bemcgarvey/CRSFtoPWM/firmware/src/sensorTask.h

/////////////////////////////////////////////////////
// Project: CRSFtoPWM                              //
// File: sensorTask.h                              //
// Target: ATSAMD21E18A                            // 
// Compiler: XC32                                  //
// Author: Brad McGarvey                           //
// License: GNU General Public License v3.0        //
// Description: sensor task handler                //
/////////////////////////////////////////////////////

#ifndef SENSORTASK_H
#define	SENSORTASK_H

#ifdef	__cplusplus
extern "C" {
#endif

    void sensorTask(void *pvParameter);

#ifdef	__cplusplus
}
#endif

#endif	/* SENSORTASK_H */
