bemcgarvey/CRSFtoPWM/firmware/src/config/default/peripheral/port/plib_port.h

/*******************************************************************************
  PORT PLIB

  Company:
    Microchip Technology Inc.

  File Name:
    plib_port.h

  Summary:
    PORT PLIB Header File

  Description:
    This file provides an interface to control and interact with PORT-I/O
    Pin controller module.

*******************************************************************************/

/*******************************************************************************
* Copyright (C) 2018 Microchip Technology Inc. and its subsidiaries.
*
* Subject to your compliance with these terms, you may use Microchip software
* and any derivatives exclusively with Microchip products. It is your
* responsibility to comply with third party license terms applicable to your
* use of third party software (including open source software) that may
* accompany Microchip software.
*
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
* IN NO EVENT WILL MICROCHIP BE LIABLE FOR ANY INDIRECT, SPECIAL, PUNITIVE,
* INCIDENTAL OR CONSEQUENTIAL LOSS, DAMAGE, COST OR EXPENSE OF ANY KIND
* WHATSOEVER RELATED TO THE SOFTWARE, HOWEVER CAUSED, EVEN IF MICROCHIP HAS
* BEEN ADVISED OF THE POSSIBILITY OR THE DAMAGES ARE FORESEEABLE. TO THE
* FULLEST EXTENT ALLOWED BY LAW, MICROCHIP'S TOTAL LIABILITY ON ALL CLAIMS IN
* ANY WAY RELATED TO THIS SOFTWARE WILL NOT EXCEED THE AMOUNT OF FEES, IF ANY,
* THAT YOU HAVE PAID DIRECTLY TO MICROCHIP FOR THIS SOFTWARE.
*******************************************************************************/

#ifndef PLIB_PORT_H
#define PLIB_PORT_H

// *****************************************************************************
// *****************************************************************************
// Section: Included Files
// *****************************************************************************
// *****************************************************************************

#include "device.h"
#include <stdint.h>
#include <stdbool.h>
#include <stddef.h>

// DOM-IGNORE-BEGIN
#ifdef __cplusplus  // Provide C++ Compatibility
    extern "C" {
#endif
// DOM-IGNORE-END

// *****************************************************************************
// *****************************************************************************
// Section: Data types and constants
// *****************************************************************************
// *****************************************************************************

/*** Macros for LED pin ***/
#define LED_Set()               (PORT_REGS->GROUP[0].PORT_OUTSET = ((uint32_t)1U << 15U))
#define LED_Clear()             (PORT_REGS->GROUP[0].PORT_OUTCLR = ((uint32_t)1U << 15U))
#define LED_Toggle()            (PORT_REGS->GROUP[0].PORT_OUTTGL = ((uint32_t)1U << 15U))
#define LED_OutputEnable()      (PORT_REGS->GROUP[0].PORT_DIRSET = ((uint32_t)1U << 15U))
#define LED_InputEnable()       (PORT_REGS->GROUP[0].PORT_DIRCLR = ((uint32_t)1U << 15U))
#define LED_Get()               (((PORT_REGS->GROUP[0].PORT_IN >> 15U)) & 0x01U)
#define LED_PIN                  PORT_PIN_PA15

// *****************************************************************************
/* PORT Group

  Summary:
    Identifies the port groups available on the device.

  Description:
    These macros identifies all the ports groups that are available on this
    device.

  Remarks:
    The caller should not use the constant expressions assigned to any of
    the preprocessor macros as these may vary between devices.

    Port groups shown here are the ones available on the selected device. Not
    all ports groups are implemented. Refer to the device specific datasheet
    for more details. The MHC will generate these macros with the port
    groups that are available on the device.
*/

/* Group 0 */
#define PORT_GROUP_0 (PORT_BASE_ADDRESS + (0U * 0x80U))


/* Helper macros to get port information from the pin */
#define GET_PORT_GROUP(pin)  ((PORT_GROUP)(PORT_BASE_ADDRESS + (0x80U * (((uint32_t)pin) >> 5U))))
#define GET_PIN_MASK(pin)   (((uint32_t)(0x1U)) << (((uint32_t)pin) & 0x1FU))

/* Named type for port group */
typedef uint32_t PORT_GROUP;


typedef enum
{
PERIPHERAL_FUNCTION_A = 0x0,
PERIPHERAL_FUNCTION_B = 0x1,
PERIPHERAL_FUNCTION_C = 0x2,
PERIPHERAL_FUNCTION_D = 0x3,
PERIPHERAL_FUNCTION_E = 0x4,
PERIPHERAL_FUNCTION_F = 0x5,
PERIPHERAL_FUNCTION_G = 0x6,
PERIPHERAL_FUNCTION_H = 0x7,

}PERIPHERAL_FUNCTION;

// *****************************************************************************
/* PORT Pins

  Summary:
    Identifies the available Ports pins.

  Description:
    This enumeration identifies all the ports pins that are available on this
    device.

  Remarks:
    The caller should not use the constant expressions assigned to any of
    the enumeration constants as these may vary between devices.

    Port pins shown here are the ones available on the selected device. Not
    all ports pins within a port group are implemented. Refer to the device
    specific datasheet for more details.
*/

typedef enum
{
    /* PA00 pin */
    PORT_PIN_PA00 = 0U,

    /* PA01 pin */
    PORT_PIN_PA01 = 1U,

    /* PA02 pin */
    PORT_PIN_PA02 = 2U,

    /* PA03 pin */
    PORT_PIN_PA03 = 3U,

    /* PA04 pin */
    PORT_PIN_PA04 = 4U,

    /* PA05 pin */
    PORT_PIN_PA05 = 5U,

    /* PA06 pin */
    PORT_PIN_PA06 = 6U,

    /* PA07 pin */
    PORT_PIN_PA07 = 7U,

    /* PA08 pin */
    PORT_PIN_PA08 = 8U,

    /* PA09 pin */
    PORT_PIN_PA09 = 9U,

    /* PA10 pin */
    PORT_PIN_PA10 = 10U,

    /* PA11 pin */
    PORT_PIN_PA11 = 11U,

    /* PA14 pin */
    PORT_PIN_PA14 = 14U,

    /* PA15 pin */
    PORT_PIN_PA15 = 15U,

    /* PA16 pin */
    PORT_PIN_PA16 = 16U,

    /* PA17 pin */
    PORT_PIN_PA17 = 17U,

    /* PA18 pin */
    PORT_PIN_PA18 = 18U,

    /* PA19 pin */
    PORT_PIN_PA19 = 19U,

    /* PA22 pin */
    PORT_PIN_PA22 = 22U,

    /* PA23 pin */
    PORT_PIN_PA23 = 23U,

    /* PA24 pin */
    PORT_PIN_PA24 = 24U,

    /* PA25 pin */
    PORT_PIN_PA25 = 25U,

    /* PA27 pin */
    PORT_PIN_PA27 = 27U,

    /* PA28 pin */
    PORT_PIN_PA28 = 28U,

    /* PA30 pin */
    PORT_PIN_PA30 = 30U,

    /* PA31 pin */
    PORT_PIN_PA31 = 31U,

    /* This element should not be used in any of the PORT APIs.
     * It will be used by other modules or application to denote that none of
     * the PORT Pin is used */
    PORT_PIN_NONE = 65535U,

} PORT_PIN;

// *****************************************************************************
// *****************************************************************************
// Section: Generated API based on pin configurations done in Pin Manager
// *****************************************************************************
// *****************************************************************************
// *****************************************************************************
/* Function:
    void PORT_Initialize(void)

  Summary:
    Initializes the PORT Library.

  Description:
    This function initializes all ports and pins as configured in the
    MHC Pin Manager.

  Precondition:
    None.

  Parameters:
    None.

  Returns:
    None.

  Example:
    <code>

    PORT_Initialize();

    </code>

  Remarks:
    The function should be called once before calling any other PORTS PLIB
    functions.
*/

void PORT_Initialize(void);

// *****************************************************************************
// *****************************************************************************
// Section: PORT APIs which operates on multiple pins of a group
// *****************************************************************************
// *****************************************************************************

// *****************************************************************************
/* Function:
    uint32_t PORT_GroupRead(PORT_GROUP group)

  Summary:
    Read all the I/O pins in the specified port group.

  Description:
    The function reads the hardware pin state of all pins in the specified group
    and returns this as a 32 bit value. Each bit in the 32 bit value represent a
    pin. For example, bit 0 in group 0 will represent pin PA0. Bit 1 will
    represent PA1 and so on. The application should only consider the value of
    the port group pins which are implemented on the device.

  Precondition:
    The PORT_Initialize() function should have been called. Input buffer
    (INEN bit in the Pin Configuration register) should be enabled in MHC.

  Parameters:
    group - One of the IO groups from the enum PORT_GROUP.

  Returns:
    A 32-bit value representing the hardware state of of all the I/O pins in the
    selected port group.

  Example:
    <code>

    uint32_t value;
    value = PORT_Read(PORT_GROUP_C);

    </code>

  Remarks:
    None.
*/

uint32_t PORT_GroupRead(PORT_GROUP group);

// *****************************************************************************
/* Function:
    uint32_t PORT_GroupLatchRead(PORT_GROUP group)

  Summary:
    Read the data driven on all the I/O pins of the selected port group.

  Description:
    The function will return a 32-bit value representing the logic levels being
    driven on the output pins within the group. The function will not sample the
    actual hardware state of the output pin. Each bit in the 32-bit return value
    will represent one of the 32 port pins within the group. The application
    should only consider the value of the pins which are available on the
    device.

  Precondition:
    The PORT_Initialize() function should have been called.

  Parameters:
    group - One of the IO groups from the enum PORT_GROUP.

  Returns:
    A 32-bit value representing the output state of of all the I/O pins in the
    selected port group.

  Example:
    <code>

    uint32_t value;
    value = PORT_GroupLatchRead(PORT_GROUP_C);

    </code>

  Remarks:
    None.
*/

uint32_t PORT_GroupLatchRead(PORT_GROUP group);

// *****************************************************************************
/* Function:
    void PORT_GroupWrite(PORT_GROUP group, uint32_t mask, uint32_t value);

  Summary:
    Write value on the masked pins of the selected port group.

  Description:
    This function writes the value contained in the value parameter to the
    port group. Port group pins which are configured for output will be updated.
    The mask parameter provides additional control on the bits in the group to
    be affected. Setting a bit to 1 in the mask will cause the corresponding
    bit in the port group to be updated. Clearing a bit in the mask will cause
    that corresponding bit in the group to stay unaffected. For example,
    setting a mask value 0xFFFFFFFF will cause all bits in the port group
    to be updated. Setting a value 0x3 will only cause port group bit 0 and
    bit 1 to be updated.

    For port pins which are not configured for output and have the pull feature
    enabled, this function will affect pull value (pull up or pull down). A bit
    value of 1 will enable the pull up. A bit value of 0 will enable the pull
    down.

  Precondition:
    The PORT_Initialize() function should have been called.

  Parameters:
    group - One of the IO groups from the enum PORT_GROUP.

    mask  - A 32 bit value in which positions of 0s and 1s decide
             which IO pins of the selected port group will be written.
             1's - Will write to corresponding IO pins.
             0's - Will remain unchanged.

    value - Value which has to be written/driven on the I/O
             lines of the selected port for which mask bits are '1'.
             Values for the corresponding mask bit '0' will be ignored.
             Refer to the function description for effect on pins
             which are not configured for output.

  Returns:
    None.

  Example:
    <code>

    PORT_GroupWrite(PORT_GROUP_C, 0x0F, 0xF563D453);

    </code>

  Remarks:
    None.
*/

void PORT_GroupWrite(PORT_GROUP group, uint32_t mask, uint32_t value);

// *****************************************************************************
/* Function:
    void PORT_GroupSet(PORT_GROUP group, uint32_t mask)

  Summary:
    Set the selected IO pins of a group.

  Description:
    This function sets (drives a logic high) on the selected output pins of a
    group. The mask parameter control the pins to be updated. A mask bit
    position with a value 1 will cause that corresponding port pin to be set. A
    mask bit position with a value 0 will cause the corresponding port pin to
    stay un-affected.

  Precondition:
    The PORT_Initialize() function should have been called.

  Parameters:
    group - One of the IO ports from the enum PORT_GROUP.
    mask - A 32 bit value in which a bit represent a pin in the group. If the
    value of the bit is 1, the corresponding port pin will driven to logic 1. If
    the value of the bit is 0. the corresponding port pin will stay un-affected.

  Returns:
    None.

  Example:
    <code>

    PORT_GroupSet(PORT_GROUP_C, 0x00A0);

    </code>

  Remarks:
    If the port pin within the the group is not configured for output and has
    the pull feature enabled, driving a logic 1 on this pin will cause the pull
    up to be enabled.
*/

void PORT_GroupSet(PORT_GROUP group, uint32_t mask);

// *****************************************************************************
/* Function:
    void PORT_GroupClear(PORT_GROUP group, uint32_t mask)

  Summary:
    Clears the selected IO pins of a group.

  Description:
    This function clears (drives a logic 0) on the selected output pins of a
    group. The mask parameter control the pins to be updated. A mask bit
    position with a value 1 will cause that corresponding port pin to be clear.
    A mask bit position with a value 0 will cause the corresponding port pin to
    stay un-affected.

  Precondition:
    The PORT_Initialize() function should have been called.

  Parameters:
    group - One of the IO ports from the enum PORT_GROUP.
    mask - A 32 bit value in which a bit represent a pin in the group. If the
    value of the bit is 1, the corresponding port pin will driven to logic 0. If
    the value of the bit is 0. the corresponding port pin will stay un-affected.

  Returns:
    None.

  Example:
    <code>

    PORT_GroupClear(PORT_GROUP_C, 0x00A0);

    </code>

  Remarks:
    If the port pin within the the group is not configured for output and has
    the pull feature enabled, driving a logic 0 on this pin will cause the pull
    down to be enabled.
*/

void PORT_GroupClear(PORT_GROUP group, uint32_t mask);

// *****************************************************************************
/* Function:
    void PORT_GroupToggle(PORT_GROUP group, uint32_t mask)

  Summary:
    Toggles the selected IO pins of a group.

  Description:
    This function toggles the selected output pins of a group. The mask
    parameter control the pins to be updated. A mask bit position with a value 1
    will cause that corresponding port pin to be toggled.  A mask bit position
    with a value 0 will cause the corresponding port pin to stay un-affected.

  Precondition:
    The PORT_Initialize() function should have been called.

  Parameters:
    group - One of the IO ports from the enum PORT_GROUP.
    mask - A 32 bit value in which a bit represent a pin in the group. If the
    value of the bit is 1, the corresponding port pin will be toggled. If the
    value of the bit is 0. the corresponding port pin will stay un-affected.

  Returns:
    None.

  Example:
    <code>

    PORT_GroupToggle(PORT_GROUP_C, 0x00A0);

    </code>

  Remarks:
    If the port pin within the the group is not configured for output and has
    the pull feature enabled, driving a logic 0 on this pin will cause the pull
    down to be enabled. Driving a logic 1 on this pin will cause the pull up to
    be enabled.
*/

void PORT_GroupToggle(PORT_GROUP group, uint32_t mask);

// *****************************************************************************
/* Function:
    void PORT_GroupInputEnable(PORT_GROUP group, uint32_t mask)

  Summary:
    Configures the selected IO pins of a group as input.

  Description:
    This function configures the selected IO pins of a group as input. The pins
    to be configured as input are selected by setting the corresponding bits in
    the mask parameter to 1.

  Precondition:
    The PORT_Initialize() function should have been called.

  Parameters:
    group - One or more of the of the IO ports from the enum PORT_GROUP.
    mask - A 32 bit value in which a bit represents a pin in the group. If the
    value of the bit is 1, the corresponding port pin will be configured as
    input. If the value of the bit is 0. the corresponding port pin will stay
    un-affected.

  Returns:
    None.

  Example:
    <code>

    PORT_GroupInputEnable(PORT_GROUP_C, 0x00A0);

    </code>

  Remarks:
   None.
*/

void PORT_GroupInputEnable(PORT_GROUP group, uint32_t mask);

// *****************************************************************************
/* Function:
    void PORT_GroupOutputEnable(PORT_GROUP group, uint32_t mask)

  Summary:
    Configures the selected IO pins of a group as output.

  Description:
    This function configures the selected IO pins of a group as output. The pins
    to be configured as output are selected by setting the corresponding bits in
    the mask parameter to 1.

  Precondition:
    The PORT_Initialize() function should have been called.

  Parameters:
    group - One or more of the of the IO ports from the enum PORT_GROUP.
    mask - A 32 bit value in which a bit represents a pin in the group. If the
    value of the bit is 1, the corresponding port pin will be configured as
    output. If the value of the bit is 0. the corresponding port pin will stay
    un-affected.

  Returns:
    None.

  Example:
    <code>

    PORT_GroupOutputEnable(PORT_GROUP_C, 0x00A0);

    </code>

  Remarks:
    None.
*/

void PORT_GroupOutputEnable(PORT_GROUP group, uint32_t mask);

// *****************************************************************************
/* Function:
    void PORT_PinPeripheralFunctionConfig(PORT_PIN pin, PERIPHERAL_FUNCTION function)

  Summary:
    Configures the peripheral function on the selected port pin

  Description:
    This function configures the selected peripheral function on the given port pin.

  Remarks:
    None
*/
void PORT_PinPeripheralFunctionConfig(PORT_PIN pin, PERIPHERAL_FUNCTION function);

// *****************************************************************************
/* Function:
    void PORT_PinGPIOConfig(PORT_PIN pin)

  Summary:
    Configures the selected pin as GPIO

  Description:
    This function configures the given pin as GPIO.

  Remarks:
    None
*/
void PORT_PinGPIOConfig(PORT_PIN pin);

// *****************************************************************************
// *****************************************************************************
// Section: PORT APIs which operates on one pin at a time
// *****************************************************************************
// *****************************************************************************

// *****************************************************************************
/* Function:
    void PORT_PinWrite(PORT_PIN pin, bool value)

  Summary:
    Writes the specified value to the selected pin.

  Description:
    This function writes/drives the "value" on the selected I/O line/pin.

  Precondition:
    The PORT_Initialize() function should have been called once.

  Parameters:
    pin - One of the IO pins from the enum PORT_PIN.
    value - value to be written on the selected pin.
            true  = set pin to high (1).
            false = clear pin to low (0).

  Returns:
    None.

  Example:
    <code>

    bool value = true;
    PORT_PinWrite(PORT_PIN_PB3, value);

    </code>

  Remarks:
    Calling this function with an input pin with the pull-up/pull-down feature
    enabled will affect the pull-up/pull-down configuration. If the value is
    false, the pull-down will be enabled. If the value is true, the pull-up will
    be enabled.
*/

static inline void PORT_PinWrite(PORT_PIN pin, bool value)
{
    PORT_GroupWrite(GET_PORT_GROUP(pin),
                    GET_PIN_MASK(pin),
                    (value ? GET_PIN_MASK(pin) : 0U));
}


// *****************************************************************************
/* Function:
    bool PORT_PinRead(PORT_PIN pin)

  Summary:
    Read the selected pin value.

  Description:
    This function reads the present state at the selected input pin.  The
    function can also be called to read the value of an output pin if input
    sampling on the output pin is enabled in MHC. If input synchronization on
    the pin is disabled in MHC, the function will cause a 2 PORT Clock cycles
    delay. Enabling the synchronization eliminates the delay but will increase
    power consumption.

  Precondition:
    The PORT_Initialize() function should have been called. Input buffer
    (INEN bit in the Pin Configuration register) should be enabled in MHC.

  Parameters:
    pin - the port pin whose state needs to be read.

  Returns:
    true - the state at the pin is a logic high.
    false - the state at the pin is a logic low.

  Example:
    <code>

    bool value;
    value = PORT_PinRead(PORT_PIN_PB3);

    </code>

  Remarks:
    None.
*/

static inline bool PORT_PinRead(PORT_PIN pin)
{
    return ((PORT_GroupRead(GET_PORT_GROUP(pin)) & GET_PIN_MASK(pin)) != 0U);
}


// *****************************************************************************
/* Function:
    bool PORT_PinLatchRead(PORT_PIN pin)

  Summary:
    Read the value driven on the selected pin.

  Description:
    This function reads the data driven on the selected I/O line/pin. The
    function does not sample the state of the hardware pin. It only returns the
    value that is written to output register. Refer to the PORT_PinRead()
    function if the state of the output pin needs to be read.

  Precondition:
    The PORT_Initialize() function should have been called.

  Parameters:
    pin - One of the IO pins from the enum PORT_PIN.

  Returns:
    true - the present value in the output latch is a logic high.
    false - the present value in the output latch is a logic low.

  Example:
    <code>

    bool value;
    value = PORT_PinLatchRead(PORT_PIN_PB3);

    </code>

  Remarks:
    To read actual pin value, PIN_Read API should be used.
*/

static inline bool PORT_PinLatchRead(PORT_PIN pin)
{
    return ((PORT_GroupLatchRead(GET_PORT_GROUP(pin)) & GET_PIN_MASK(pin)) != 0U);
}


// *****************************************************************************
/* Function:
    void PORT_PinToggle(PORT_PIN pin)

  Summary:
    Toggles the selected pin.

  Description:
    This function toggles/inverts the present value on the selected I/O line/pin.

  Precondition:
    The PORT_Initialize() function should have been called.

  Parameters:
    pin - One of the IO pins from the enum PORT_PIN.

  Returns:
    None.

  Example:
    <code>

    PORT_PinToggle(PORT_PIN_PB3);

    </code>

  Remarks:
    None.
*/

static inline void PORT_PinToggle(PORT_PIN pin)
{
    PORT_GroupToggle(GET_PORT_GROUP(pin), GET_PIN_MASK(pin));
}


// *****************************************************************************
/* Function:
    void PORT_PinSet(PORT_PIN pin)

  Summary:
    Sets the selected pin.

  Description:
    This function drives a logic 1 on the selected I/O line/pin.

  Precondition:
    The PORT_Initialize() function should have been called.

  Parameters:
    pin - One of the IO pins from the enum PORT_PIN.

  Returns:
    None.

  Example:
    <code>

    PORT_PinSet(PORT_PIN_PB3);

    </code>

  Remarks:
    None.
*/

static inline void PORT_PinSet(PORT_PIN pin)
{
    PORT_GroupSet(GET_PORT_GROUP(pin), GET_PIN_MASK(pin));
}


// *****************************************************************************
/* Function:
    void PORT_PinClear(PORT_PIN pin)

  Summary:
    Clears the selected pin.

  Description:
    This function drives a logic 0 on the selected I/O line/pin.

  Precondition:
    The PORT_Initialize() function should have been called.

  Parameters:
    pin - One of the IO pins from the enum PORT_PIN.

  Returns:
    None.

  Example:
    <code>

    PORT_PinClear(PORT_PIN_PB3);

    </code>

  Remarks:
    None.
*/

static inline void PORT_PinClear(PORT_PIN pin)
{
    PORT_GroupClear(GET_PORT_GROUP(pin), GET_PIN_MASK(pin));
}


// *****************************************************************************
/* Function:
    void PORT_PinInputEnable(PORT_PIN pin)

  Summary:
    Configures the selected IO pin as input.

  Description:
    This function configures the selected IO pin as input. This function
    override the MHC input output pin settings.

  Precondition:
    The PORT_Initialize() function should have been called.

  Parameters:
    pin - One of the IO pins from the enum PORT_PIN.

  Returns:
    None.

  Example:
    <code>

    PORT_PinInputEnable(PORT_PIN_PB3);

    </code>

  Remarks:
    None.
*/

static inline void PORT_PinInputEnable(PORT_PIN pin)
{
    PORT_GroupInputEnable(GET_PORT_GROUP(pin), GET_PIN_MASK(pin));
}


// *****************************************************************************
/* Function:
    void PORT_PinOutputEnable(PORT_PIN pin)

  Summary:
    Enables selected IO pin as output.

  Description:
    This function enables selected IO pin as output. Calling this function will
    override the MHC input output pin configuration.

  Precondition:
    The PORT_Initialize() function should have been called.

  Parameters:
    pin - One of the IO pins from the enum PORT_PIN.

  Returns:
    None.

  Example:
    <code>

    PORT_PinOutputEnable(PORT_PIN_PB3);

    </code>

  Remarks:
    None.
*/

static inline void PORT_PinOutputEnable(PORT_PIN pin)
{
    PORT_GroupOutputEnable(GET_PORT_GROUP(pin), GET_PIN_MASK(pin));
}

// DOM-IGNORE-BEGIN
#ifdef __cplusplus  // Provide C++ Compatibility

}

#endif
// DOM-IGNORE-END
#endif // PLIB_PORT_H
