bemcgarvey/CRSFtoPWM/firmware/src/config/default/peripheral/adc/plib_adc.c

/*******************************************************************************
  Analog-to-Digital Converter(ADC) PLIB

  Company
    Microchip Technology Inc.

  File Name
    plib_adc.c

  Summary
    ADC PLIB Implementation File.

  Description
    This file defines the interface to the ADC peripheral library. This
    library provides access to and control of the associated peripheral
    instance.

  Remarks:
    None.

*******************************************************************************/

// DOM-IGNORE-BEGIN
/*******************************************************************************
* Copyright (C) 2018 Microchip Technology Inc. and its subsidiaries.
*
* Subject to your compliance with these terms, you may use Microchip software
* and any derivatives exclusively with Microchip products. It is your
* responsibility to comply with third party license terms applicable to your
* use of third party software (including open source software) that may
* accompany Microchip software.
*
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
* IN NO EVENT WILL MICROCHIP BE LIABLE FOR ANY INDIRECT, SPECIAL, PUNITIVE,
* INCIDENTAL OR CONSEQUENTIAL LOSS, DAMAGE, COST OR EXPENSE OF ANY KIND
* WHATSOEVER RELATED TO THE SOFTWARE, HOWEVER CAUSED, EVEN IF MICROCHIP HAS
* BEEN ADVISED OF THE POSSIBILITY OR THE DAMAGES ARE FORESEEABLE. TO THE
* FULLEST EXTENT ALLOWED BY LAW, MICROCHIP'S TOTAL LIABILITY ON ALL CLAIMS IN
* ANY WAY RELATED TO THIS SOFTWARE WILL NOT EXCEED THE AMOUNT OF FEES, IF ANY,
* THAT YOU HAVE PAID DIRECTLY TO MICROCHIP FOR THIS SOFTWARE.
*******************************************************************************/
// DOM-IGNORE-END

// *****************************************************************************
// *****************************************************************************
// Section: Included Files
// *****************************************************************************
// *****************************************************************************
/* This section lists the other files that are included in this file.
*/

#include "plib_adc.h"
#include "interrupts.h"

// *****************************************************************************
// *****************************************************************************
// Section: Global Data
// *****************************************************************************
// *****************************************************************************

#define ADC_LINEARITY0_POS  (27U)
#define ADC_LINEARITY0_Msk   ((0x1FUL << ADC_LINEARITY0_POS))

#define ADC_LINEARITY1_POS  (0U)
#define ADC_LINEARITY1_Msk   ((0x7U << ADC_LINEARITY1_POS))

#define ADC_BIASCAL_POS  (3U)
#define ADC_BIASCAL_Msk   ((0x7U << ADC_BIASCAL_POS))

// *****************************************************************************
// *****************************************************************************
// Section: ADC Implementation
// *****************************************************************************
// *****************************************************************************

// *****************************************************************************
/* Initialize ADC module */
void ADC_Initialize( void )
{
    /* Reset ADC */
    ADC_REGS->ADC_CTRLA = ADC_CTRLA_SWRST_Msk;

    while((ADC_REGS->ADC_STATUS & ADC_STATUS_SYNCBUSY_Msk)!= 0U)
    {
        /* Wait for Synchronization */
    }

    uint32_t adc_linearity0 = (((*(uint32_t*)OTP4_ADDR) & ADC_LINEARITY0_Msk) >> ADC_LINEARITY0_POS);
    uint32_t adc_linearity1 = (((*(uint32_t*)(OTP4_ADDR + 4U)) & ADC_LINEARITY1_Msk) >> ADC_LINEARITY1_POS);

    /* Write linearity calibration and bias calibration */
    ADC_REGS->ADC_CALIB = (uint16_t)((ADC_CALIB_LINEARITY_CAL(adc_linearity0 | (adc_linearity1 << 5U))) \
        | ADC_CALIB_BIAS_CAL((((*(uint32_t*)(OTP4_ADDR + 4U)) & ADC_BIASCAL_Msk) >> ADC_BIASCAL_POS)));

    /* Sampling length */
    ADC_REGS->ADC_SAMPCTRL = ADC_SAMPCTRL_SAMPLEN(3U);

    /* reference */
    ADC_REGS->ADC_REFCTRL = ADC_REFCTRL_REFSEL_INTVCC1;

    /* positive and negative input pins */
    ADC_REGS->ADC_INPUTCTRL = (uint32_t) ADC_POSINPUT_PIN0 | (uint32_t) ADC_NEGINPUT_GND \
        | ADC_INPUTCTRL_INPUTSCAN(0U) | ADC_INPUTCTRL_INPUTOFFSET(0U) | ADC_INPUTCTRL_GAIN_DIV2;
    while((ADC_REGS->ADC_STATUS & ADC_STATUS_SYNCBUSY_Msk)!= 0U)
    {
        /* Wait for Synchronization */
    }

    /* Prescaler, Resolution & Operation Mode */
    ADC_REGS->ADC_CTRLB = ADC_CTRLB_PRESCALER_DIV64 | ADC_CTRLB_RESSEL_12BIT ;
    while((ADC_REGS->ADC_STATUS & ADC_STATUS_SYNCBUSY_Msk)!= 0U)
    {
        /* Wait for Synchronization */
    }

    /* Clear all interrupt flags */
    ADC_REGS->ADC_INTFLAG = ADC_INTFLAG_Msk;

    while((ADC_REGS->ADC_STATUS & ADC_STATUS_SYNCBUSY_Msk) != 0U)
    {
        /* Wait for Synchronization */
    }
}

/* Enable ADC module */
void ADC_Enable( void )
{
    ADC_REGS->ADC_CTRLA |= ADC_CTRLA_ENABLE_Msk;
    while((ADC_REGS->ADC_STATUS & ADC_STATUS_SYNCBUSY_Msk) != 0U)
    {
        /* Wait for Synchronization */
    }
}

/* Disable ADC module */
void ADC_Disable( void )
{
    ADC_REGS->ADC_CTRLA = ((ADC_REGS->ADC_CTRLA) & (uint8_t)(~ADC_CTRLA_ENABLE_Msk));
    while((ADC_REGS->ADC_STATUS & ADC_STATUS_SYNCBUSY_Msk) != 0U)
    {
        /* Wait for Synchronization */
    }
}

/* Configure channel input */
void ADC_ChannelSelect( ADC_POSINPUT positiveInput, ADC_NEGINPUT negativeInput )
{
    /* Configure positive and negative input pins */
    uint32_t channel;
    channel = ADC_REGS->ADC_INPUTCTRL;
    channel &= ~(ADC_INPUTCTRL_MUXPOS_Msk | ADC_INPUTCTRL_MUXNEG_Msk);
    channel |= (uint32_t) positiveInput | (uint32_t) negativeInput;
    ADC_REGS->ADC_INPUTCTRL = channel;

    while((ADC_REGS->ADC_STATUS & ADC_STATUS_SYNCBUSY_Msk) != 0U)
    {
        /* Wait for Synchronization */
    }
}

/* Start the ADC conversion by SW */
void ADC_ConversionStart( void )
{
    /* Start conversion */
    ADC_REGS->ADC_SWTRIG |= ADC_SWTRIG_START_Msk;

    while((ADC_REGS->ADC_STATUS & ADC_STATUS_SYNCBUSY_Msk) != 0U)
    {
        /* Wait for Synchronization */
    }
}

/* Configure window comparison threshold values */
void ADC_ComparisonWindowSet(uint16_t low_threshold, uint16_t high_threshold)
{
    ADC_REGS->ADC_WINLT = low_threshold;
    while((ADC_REGS->ADC_STATUS & ADC_STATUS_SYNCBUSY_Msk) != 0U)
    {
        /* Wait for Synchronization */
    }    
    ADC_REGS->ADC_WINUT = high_threshold;
    while((ADC_REGS->ADC_STATUS & ADC_STATUS_SYNCBUSY_Msk) != 0U)
    {
        /* Wait for Synchronization */
    }
}

void ADC_WindowModeSet(ADC_WINMODE mode)
{
    ADC_REGS->ADC_WINCTRL = (uint8_t)mode << ADC_WINCTRL_WINMODE_Pos;
    while((ADC_REGS->ADC_STATUS & ADC_STATUS_SYNCBUSY_Msk) != 0U)
    {
        /* Wait for Synchronization */
    }
}


/* Read the conversion result */
uint16_t ADC_ConversionResultGet( void )
{
    return (uint16_t)ADC_REGS->ADC_RESULT;
}

void ADC_InterruptsClear(ADC_STATUS interruptMask)
{
    ADC_REGS->ADC_INTFLAG = interruptMask;
}

void ADC_InterruptsEnable(ADC_STATUS interruptMask)
{
    ADC_REGS->ADC_INTENSET = interruptMask;
}

void ADC_InterruptsDisable(ADC_STATUS interruptMask)
{
    ADC_REGS->ADC_INTENCLR = interruptMask;
}


/* Check whether result is ready */
bool ADC_ConversionStatusGet( void )
{
    bool status;
    status =  (((ADC_REGS->ADC_INTFLAG & ADC_INTFLAG_RESRDY_Msk) >> ADC_INTFLAG_RESRDY_Pos)!= 0U);
    if (status == true)
    {
        ADC_REGS->ADC_INTFLAG = ADC_INTFLAG_RESRDY_Msk;
    }
    return status;
}
