bemcgarvey/CRSFtoPWM/firmware/src/passthrough.c

/////////////////////////////////////////////////////
// Project: CRSFtoPWM                              //
// File: passthrough.c                             //
// Target: ATSAMD21E18A                            // 
// Compiler: XC32                                  //
// Author: Brad McGarvey                           //
// License: GNU General Public License v3.0        //
// Description: BetaFlight passthrough functions   //
/////////////////////////////////////////////////////

#include "definitions.h"
#include "passthrough.h"
#include "stdio.h"
#include "rtosHandles.h"
#include "crsf.h"
#include "crsf_uart.h"
#include "settings.h"
#include "usart.h"

TaskHandle_t passthroughTaskHandle;
QueueHandle_t passthroughQueueS0toS1;
QueueHandle_t passthroughQueueS1toS0;
volatile bool passthroughEnabled = false;

static bool CLIecho = false;
static char commandLine[64];

void handleSerialCommand(void);

void passthroughTask(void *pvParameters) {
    char rxByte;
    int pos = 0;
    char newline = '\n';
    NVIC_SetPriority(SERCOM1_IRQn, 1);
    passthroughQueueS0toS1 = xQueueCreate(256, 1);
    passthroughQueueS1toS0 = xQueueCreate(256, 1);
    while (1) {
        while (!SERCOM1_USART_Read(&rxByte, 1));
        if (CLIecho && rxByte != '\n') {
            SERCOM1_USART_Write(&rxByte, 1);
        }
        if (rxByte == '\r') {
            if (pos != 0) {
                SERCOM1_USART_Write(&newline, 1);
                commandLine[pos] = '\0';
                handleSerialCommand();
                pos = 0;
            }
        } else if (rxByte == '\n') {
            pos = 0;
        } else {
            commandLine[pos] = rxByte;
            ++pos;
            if (pos >= 64) {
                pos = 0;
            }
        }
    }
}

void handleSerialCommand(void) {
    bool prompt = true;
    if (strncmp(commandLine, "#", 1) == 0) {
        vTaskSuspend(sensorTaskHandle);
        printf("CLI Mode, type 'exit' or 'help'\r\n");
        CLIecho = true;
    } else if (strncmp(commandLine, "serial", 64) == 0) {
        printf("serial 0 64 0 0 0 0\r\n");
    } else if (strncmp(commandLine, "get serialrx_provider", 64) == 0) {
        printf("serialrx_provider = CRSF\r\n");
    } else if (strncmp(commandLine, "get serialrx_inverted", 64) == 0) {
        printf("serialrx_inverted = OFF\r\n");
    } else if (strncmp(commandLine, "get serialrx_halfduplex", 64) == 0) {
        printf("serialrx_halfduplex = OFF\r\n");
    } else if (strncmp(commandLine, "serialpassthrough 0 ", 20) == 0) {
        LED_Set();
        passthroughEnabled = true;
        WDT_Disable();
        switchSERCOM1Baud(BAUD_420000);
        SERCOM1_REGS->USART_INT.SERCOM_INTENSET = (uint8_t) (SERCOM_USART_INT_INTENSET_ERROR_Msk | SERCOM_USART_INT_INTENSET_RXC_Msk);
        NVIC_EnableIRQ(SERCOM1_IRQn);
        vTaskSuspend(watchdogTaskHandle);
        vTaskSuspend(rxTaskHandle);
        if (settings.sBusEnabled) {
            vTaskSuspend(sbusTaskHandle);
        }
        lastByteTick = 0;
        while (passthroughEnabled) {
            uint8_t temp;
            if (xQueueReceive(passthroughQueueS0toS1, &temp, 0) == pdTRUE && (SERCOM1_REGS->USART_INT.SERCOM_INTFLAG & (uint8_t) SERCOM_USART_INT_INTFLAG_DRE_Msk)) {
                SERCOM1_REGS->USART_INT.SERCOM_DATA = temp;
            }
            if (xQueueReceive(passthroughQueueS1toS0, &temp, 0) == pdTRUE && (SERCOM0_REGS->USART_INT.SERCOM_INTFLAG & (uint8_t) SERCOM_USART_INT_INTFLAG_DRE_Msk)) {
                SERCOM0_REGS->USART_INT.SERCOM_DATA = temp;
            }
            if (lastByteTick >= 6000) {
                passthroughEnabled = false;
            }
        }
        NVIC_DisableIRQ(SERCOM1_IRQn);
        SERCOM1_REGS->USART_INT.SERCOM_INTENCLR = (uint8_t) (SERCOM_USART_INT_INTENSET_ERROR_Msk | SERCOM_USART_INT_INTENSET_RXC_Msk);
        switchSERCOM1Baud(BAUD_115200);
        vTaskResume(watchdogTaskHandle);
        vTaskResume(rxTaskHandle);
        if (settings.sBusEnabled) {
            vTaskResume(sbusTaskHandle);
        }
        vTaskResume(sensorTaskHandle);
        WDT_Enable();
        LED_Clear();
    } else {
        prompt = false;
    }
    if (prompt) {
        printf("# ");
    }
}

void passthroughISR(void) {
    uint8_t temp;
    temp = SERCOM1_REGS->USART_INT.SERCOM_DATA;
    xQueueSendToBackFromISR(passthroughQueueS1toS0, &temp, NULL);
    lastByteTick = 0;
}
