bemcgarvey/CRSFtoPWM/firmware/src/usart.c

/////////////////////////////////////////////////////
// Project: CRSFtoPWM                              //
// File: usart.c                                   //
// Target: ATSAMD21E18A                            // 
// Compiler: XC32                                  //
// Author: Brad McGarvey                           //
// License: GNU General Public License v3.0        //
// Description: SERCOM1 usart ISR                  //
/////////////////////////////////////////////////////

#include "definitions.h"
#include "usart.h"
#include "settings.h"
#include "passthrough.h"
#include "gps.h"

#define BAUD_VALUE_420000           (56360UL)
#define BAUD_VALUE_115200           (63019UL)
#define BAUD_VALUE_9600             (65326UL)
#define BAUD_VALUE_19200            (65117UL)
#define BAUD_VALUE_38400            (64697UL)
#define BAUD_VALUE_57600            (64278UL)

void switchSERCOM1Baud(SERCOM1_Baud baud) {
    //disable
    SERCOM1_REGS->USART_INT.SERCOM_CTRLA &= ~SERCOM_USART_INT_CTRLA_ENABLE_Msk;
    while ((SERCOM1_REGS->USART_INT.SERCOM_SYNCBUSY) != 0U);
    switch (baud) {
        case BAUD_420000:
            SERCOM1_REGS->USART_INT.SERCOM_BAUD = (uint16_t) SERCOM_USART_INT_BAUD_BAUD(BAUD_VALUE_420000);
            break;
        case BAUD_115200:
            SERCOM1_REGS->USART_INT.SERCOM_BAUD = (uint16_t) SERCOM_USART_INT_BAUD_BAUD(BAUD_VALUE_115200);
            break;
        case BAUD_9600:
            SERCOM1_REGS->USART_INT.SERCOM_BAUD = (uint16_t) SERCOM_USART_INT_BAUD_BAUD(BAUD_VALUE_9600);
            break;
        case BAUD_19200:
            SERCOM1_REGS->USART_INT.SERCOM_BAUD = (uint16_t) SERCOM_USART_INT_BAUD_BAUD(BAUD_VALUE_19200);
            break;
        case BAUD_38400:
            SERCOM1_REGS->USART_INT.SERCOM_BAUD = (uint16_t) SERCOM_USART_INT_BAUD_BAUD(BAUD_VALUE_38400);
            break;
        case BAUD_57600:
            SERCOM1_REGS->USART_INT.SERCOM_BAUD = (uint16_t) SERCOM_USART_INT_BAUD_BAUD(BAUD_VALUE_57600);
            break;
    }
    while ((SERCOM1_REGS->USART_INT.SERCOM_SYNCBUSY) != 0U);
    //Enable
    SERCOM1_REGS->USART_INT.SERCOM_CTRLA |= SERCOM_USART_INT_CTRLA_ENABLE_Msk;
    while ((SERCOM1_REGS->USART_INT.SERCOM_SYNCBUSY) != 0U);
}

void SERCOM1_USART_ErrorClear( void );

void SERCOM1_USART_InterruptHandler(void) {
    uint8_t testCondition;
    testCondition = SERCOM1_REGS->USART_INT.SERCOM_INTFLAG & SERCOM_USART_INT_INTFLAG_ERROR_Msk;
    if (testCondition) {
        SERCOM1_USART_ErrorClear();
        return;
    }
    testCondition = SERCOM1_REGS->USART_INT.SERCOM_INTFLAG & SERCOM_USART_INT_INTFLAG_RXC_Msk;
    if (testCondition) {
        if (settings.uartMode == UART_PASSTHROUGH) {
            passthroughISR();
        } else if (settings.uartMode == UART_GPS) {
            gpsISR();
        }
    }
}
