bemcgarvey/CRSFtoPWM/firmware/src/version.h

/////////////////////////////////////////////////////
// Project: CRSFtoPWM                              //
// File: version.h                                 //
// Target: ATSAMD21E18A                            // 
// Compiler: XC32                                  //
// Author: Brad McGarvey                           //
// License: GNU General Public License v3.0        //
// Description: firmware version definition        //
/////////////////////////////////////////////////////

#ifndef VERSION_H
#define	VERSION_H

#ifdef	__cplusplus
extern "C" {
#endif

#define MAJOR_VERSION   1
#define MINOR_VERSION   3
    
    extern uint16_t version;


#ifdef	__cplusplus
}
#endif

#endif	/* VERSION_H */
