bemcgarvey/CRSFtoPWM/firmware/src/tasks.c

/////////////////////////////////////////////////////
// Project: CRSFtoPWM                              //
// File: tasks.c                                   //
// Target: ATSAMD21E18A                            // 
// Compiler: XC32                                  //
// Author: Brad McGarvey                           //
// License: GNU General Public License v3.0        //
// Description: task creation                      //
/////////////////////////////////////////////////////

#include "definitions.h"
#include "tasks.h"
#include "rtosHandles.h"
#include "statusTask.h"
#include "sensorTask.h"
#include "rxTask.h"
#include "debug.h"
#include "crsf.h"
#include "settings.h"
#include "sbusTask.h"
#include "watchdogTask.h"
#include "passthrough.h"
#include "gps.h"

bool wdtResetHappened;

QueueHandle_t debugQueue;
QueueHandle_t packetQueue;

void initTasks(void) {
    xTaskCreate(statusTask, "statusTask", 128, NULL, 1, &statusTaskHandle);
    if (!wdtResetHappened) {
        xTaskCreate(sensorTask, "sensorTask", 512, NULL, 2, &sensorTaskHandle);
        if (settings.uartMode == UART_PASSTHROUGH) {
            xTaskCreate(passthroughTask, "passthroughTask", 512, NULL, 1, &passthroughTaskHandle);
        } else if (settings.uartMode == UART_GPS) {
            xTaskCreate(gpsTask, "gpsTask", 512, NULL, 1, &gpsTaskHandle);
            sentenceQueueHandle = xQueueCreate(5, sizeof (char *));
            gpsPacketQueueHandle = xQueueCreate(1, sizeof (CRSF_sensor_gps));
        }
    }
    xTaskCreate(rxTask, "rxTask", 512, NULL, 4, &rxTaskHandle);
    xTaskCreate(watchdogTask, "watchdogTask", 128, NULL, 1, &watchdogTaskHandle);
    if (settings.sBusEnabled) {
        xTaskCreate(sbusTask, "sbusTask", 512, NULL, 3, &sbusTaskHandle);
    }
    debugQueue = xQueueCreate(5, DEBUG_MAX_MSG_LEN);
    packetQueue = xQueueCreate(1, CHANNEL_PACKET_LEN);
    WDT_Enable();
    vTaskStartScheduler();
}
