bemcgarvey/CRSFtoPWM/firmware/src/sbusTask.h

/////////////////////////////////////////////////////
// Project: CRSFtoPWM                              //
// File: sbusTask.h                                //
// Target: ATSAMD21E18A                            // 
// Compiler: XC32                                  //
// Author: Brad McGarvey                           //
// License: GNU General Public License v3.0        //
// Description: sBus task handler                  //
/////////////////////////////////////////////////////

#ifndef SBUSTASK_H
#define	SBUSTASK_H

#ifdef	__cplusplus
extern "C" {
#endif


void sbusTask(void *pvParameters);

#ifdef	__cplusplus
}
#endif

#endif	/* SBUSTASK_H */
