bemcgarvey/CRSFtoPWM/firmware/src/statusTask.h

/////////////////////////////////////////////////////
// Project: CRSFtoPWM                              //
// File: statusTask.h                              //
// Target: ATSAMD21E18A                            // 
// Compiler: XC32                                  //
// Author: Brad McGarvey                           //
// License: GNU General Public License v3.0        //
// Description: status task handler                //
/////////////////////////////////////////////////////

#ifndef STATUSTASK_H
#define	STATUSTASK_H

#ifdef	__cplusplus
extern "C" {
#endif

void statusTask(void *pvParameters);


#ifdef	__cplusplus
}
#endif

#endif	/* STATUSTASK_H */
