bemcgarvey/CRSFtoPWM/firmware/src/watchdogTask.h

/////////////////////////////////////////////////////
// Project: CRSFtoPWM                              //
// File: watchdogTask.h                            //
// Target: ATSAMD21E18A                            // 
// Compiler: XC32                                  //
// Author: Brad McGarvey                           //
// License: GNU General Public License v3.0        //
// Description: watchdog task handler              //
/////////////////////////////////////////////////////

#ifndef WATCHDOGTASK_H
#define	WATCHDOGTASK_H

#ifdef	__cplusplus
extern "C" {
#endif

void watchdogTask(void *pvParameters);

#ifdef	__cplusplus
}
#endif

#endif	/* WATCHDOGTASK_H */
