bemcgarvey/CRSFtoPWM/software/CRSFClient/aboutdialog.cpp

#include "aboutdialog.h"
#include "ui_aboutdialog.h"

AboutDialog::AboutDialog(QWidget *parent) :
    QDialog(parent),
    ui(new Ui::AboutDialog)
{
    setWindowFlags(Qt::Dialog | Qt::CustomizeWindowHint | Qt::WindowTitleHint | Qt::WindowCloseButtonHint | Qt::MSWindowsFixedSizeDialogHint);
    ui->setupUi(this);
}

AboutDialog::~AboutDialog()
{
    delete ui;
}

void AboutDialog::on_pushButton_clicked()
{
    close();
}
